knowledgetechnologyuhh/NICO-cad/stl files/ear_right.STL

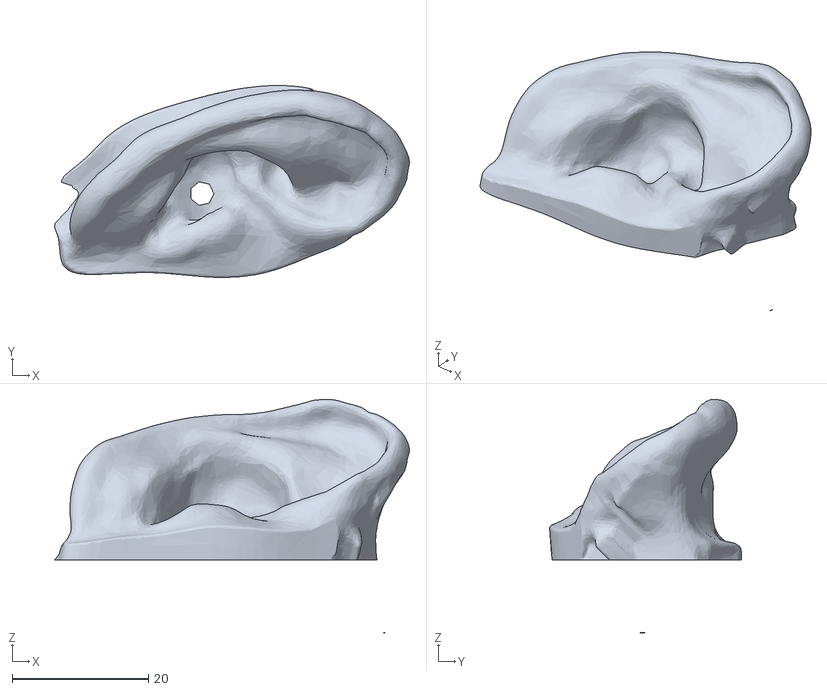
[picture p20: CAD file, 2020-01-28]
stl files/ear_right.STL
52.2 x 28.2 x 34.3
