knowledgetechnologyuhh/NICO-cad/Optimized for SLS/grommet.stl

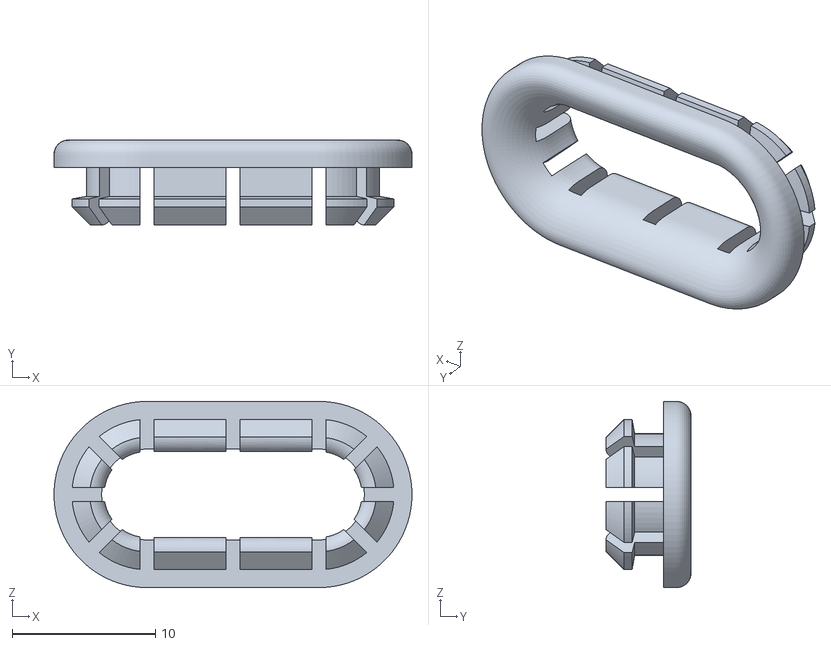
[picture p21: CAD file, 2019-10-23]
Optimized for SLS/grommet.stl
25.0 x 5.93 x 13.0
