knowledgetechnologyuhh/NICO-cad/Optimized for SLS/head_cable_clamp.stl

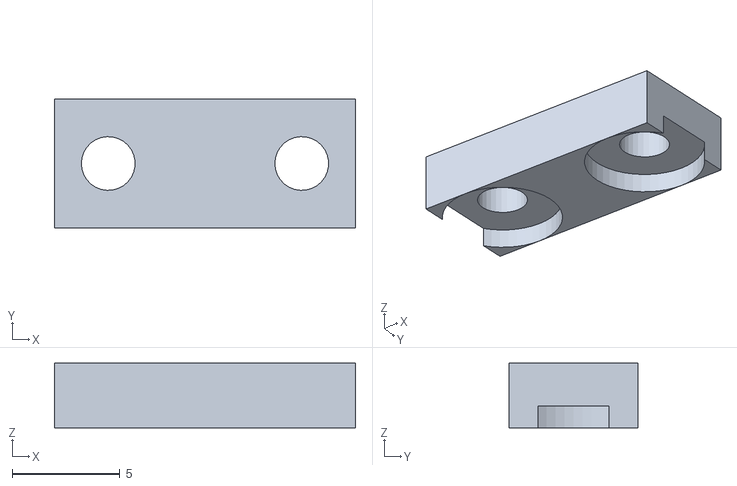
[picture p22: CAD file, 2019-10-23]
Optimized for SLS/head_cable_clamp.stl
14.0 x 6.00 x 3.00
