knowledgetechnologyuhh/NICO-cad/stl files/FR05-S101.stl

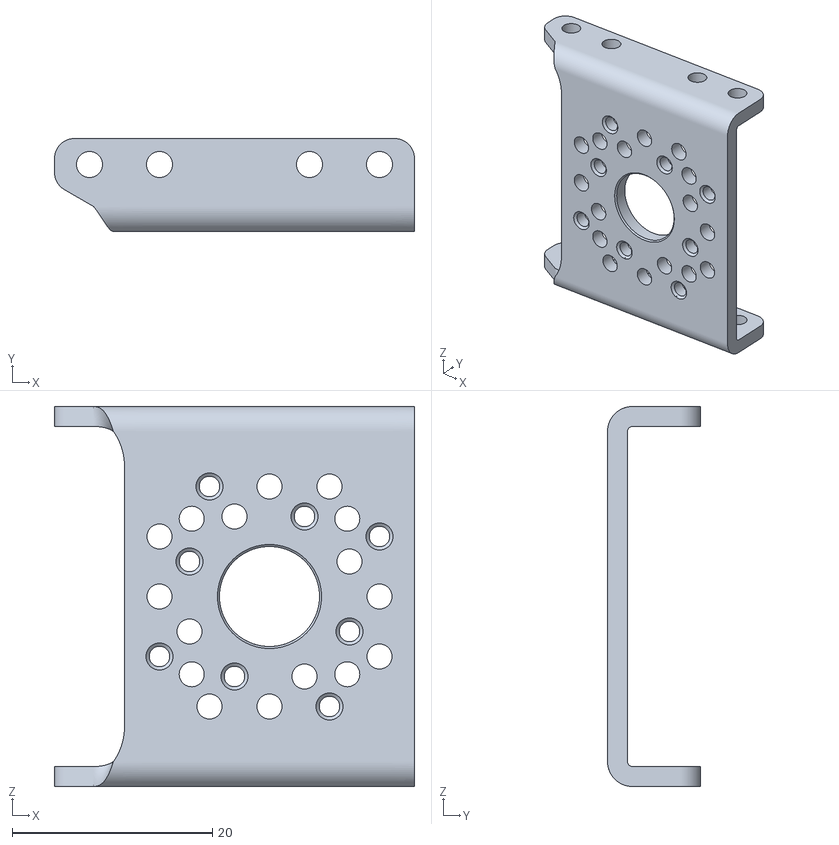
[picture p23: CAD file, 2020-01-28]
stl files/FR05-S101.stl
36.0 x 9.30 x 38.0
