knowledgetechnologyuhh/NICO-cad/Optimized for SLS/upper plate.dxf

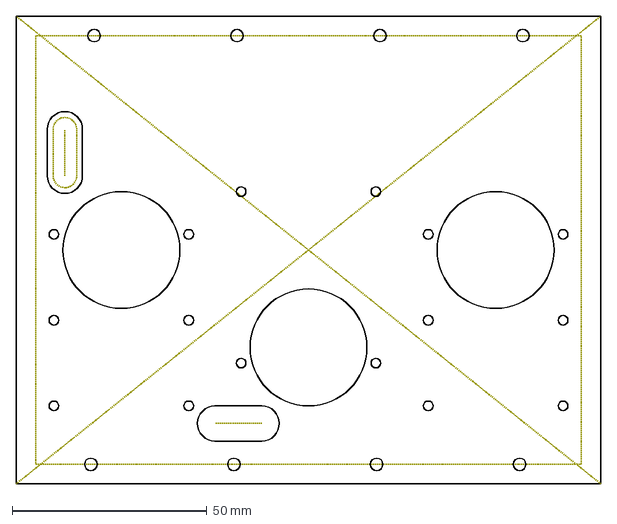
[picture p24: CAD file, 2019-10-23]
Optimized for SLS/upper plate.dxf
150.0 x 120.0 mm
