knowledgetechnologyuhh/NICO-cad/stl files/headnickholder_long.stl

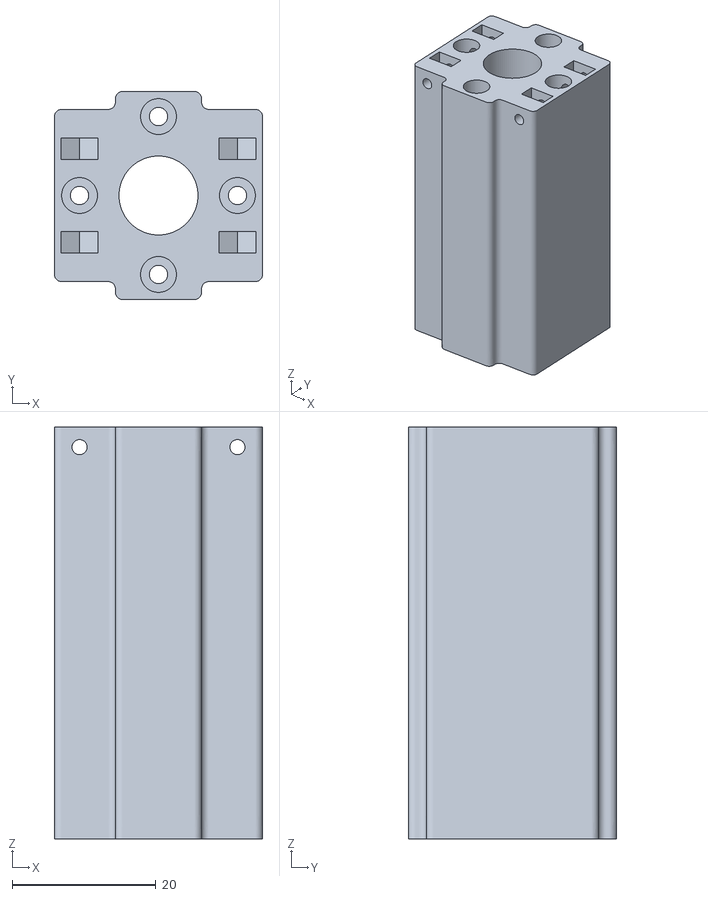
[picture p25: CAD file, 2020-01-28]
stl files/headnickholder_long.stl
29.0 x 29.0 x 57.4
