knowledgetechnologyuhh/NICO-cad/Optimized for SLS/head_support.stl

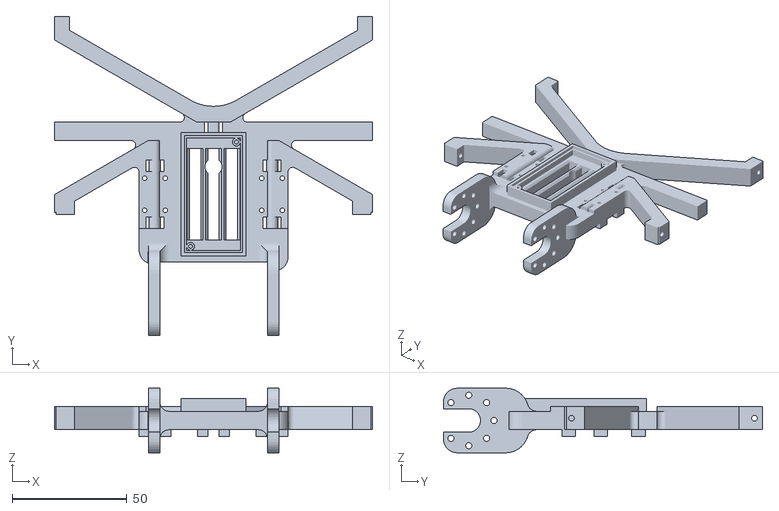
[picture p26: CAD file, 2019-10-23]
Optimized for SLS/head_support.stl
138.7 x 139.1 x 28.2
