knowledgetechnologyuhh/NICO-cad/stl files/lower_arm_thick.stl

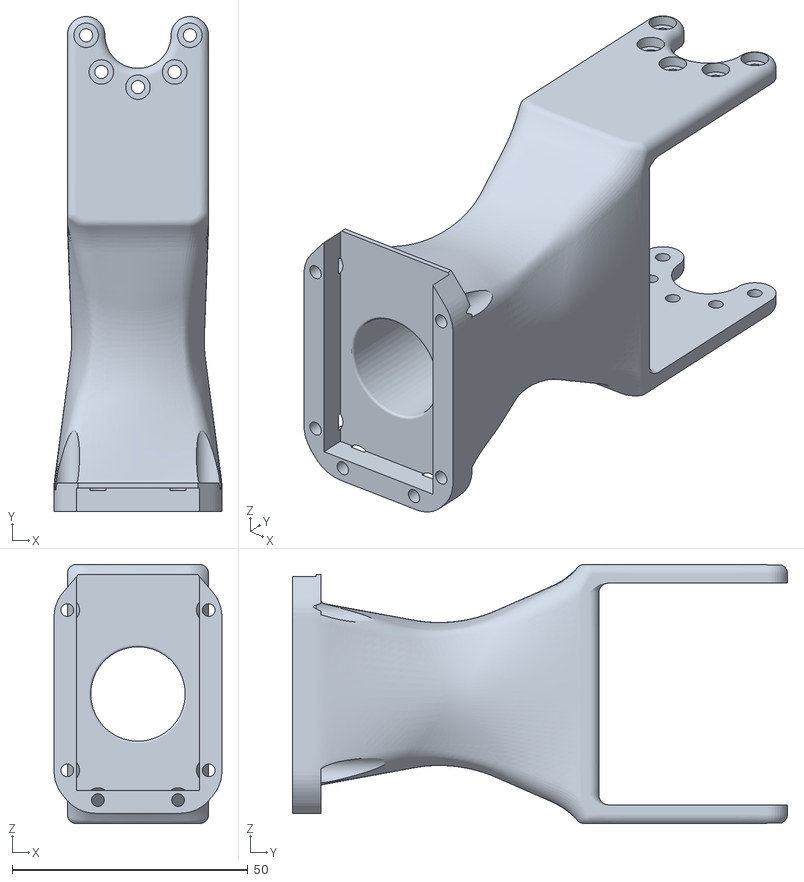
[picture p27: CAD file, 2020-01-28]
stl files/lower_arm_thick.stl
35.6 x 105.0 x 55.0
