knowledgetechnologyuhh/NICO-cad/Optimized for SLS/shoulder.stl

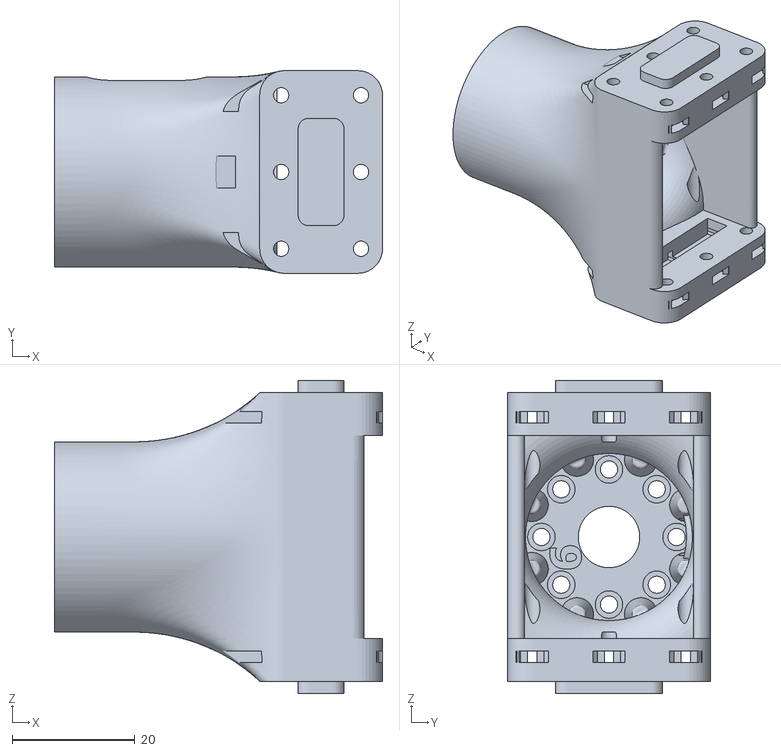
[picture p28: CAD file, 2019-10-23]
Optimized for SLS/shoulder.stl
53.4 x 33.0 x 51.0
