knowledgetechnologyuhh/NICO-cad/stl files/connector.stl

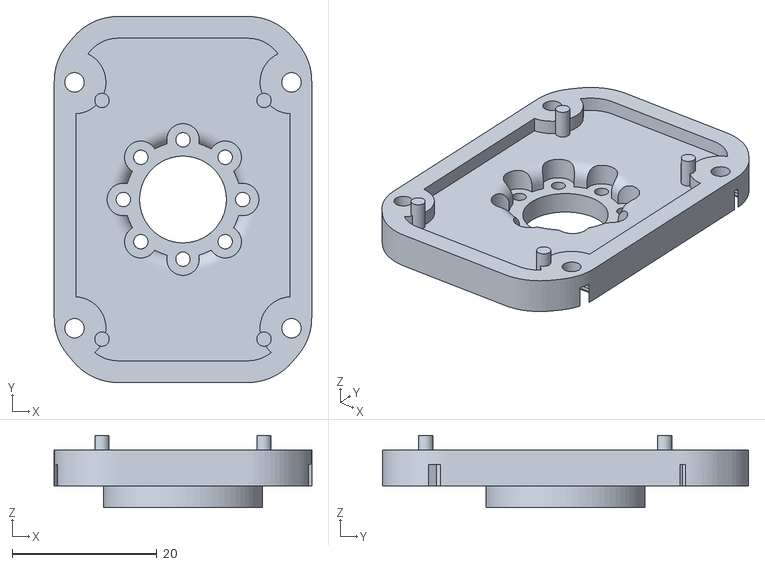
[picture p29: CAD file, 2020-01-28]
stl files/connector.stl
35.6 x 50.6 x 10.0
