knowledgetechnologyuhh/NICO-cad/Optimized for SLS/lower_arm.stl

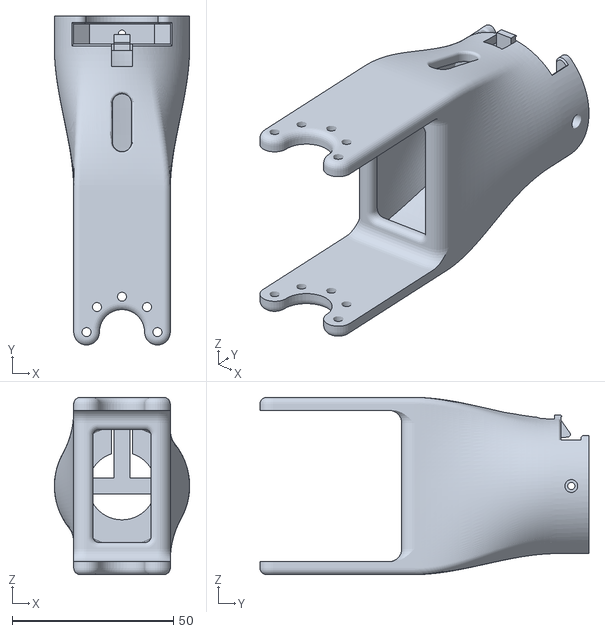
[picture p30: CAD file, 2019-10-23]
Optimized for SLS/lower_arm.stl
42.0 x 102.1 x 55.0
