knowledgetechnologyuhh/NICO-cad/stl files/spider.stl

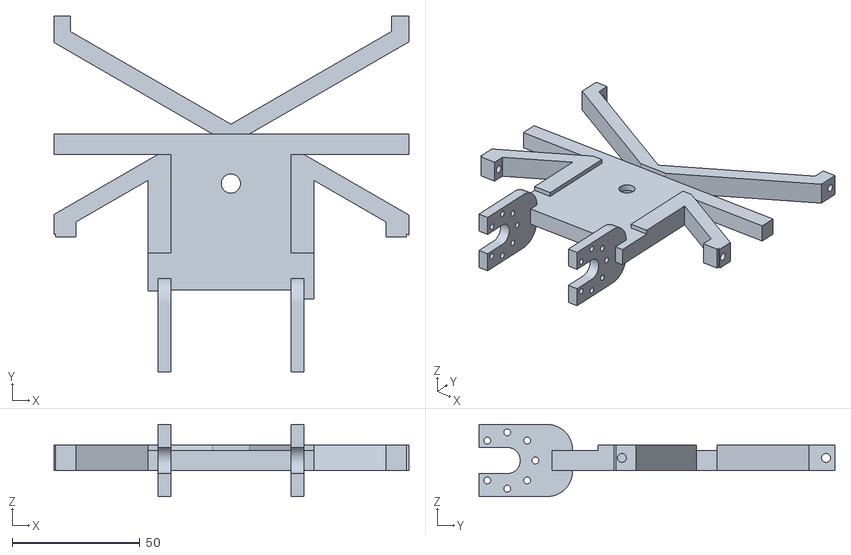
[picture p31: CAD file, 2019-03-22]
stl files/spider.stl
138.7 x 139.1 x 28.2
