knowledgetechnologyuhh/NICO-cad/Optimized for SLS/shoulder_spacer.stl

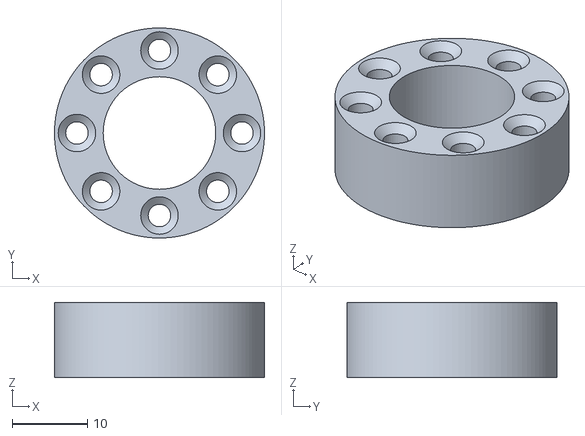
[picture p32: CAD file, 2019-10-23]
Optimized for SLS/shoulder_spacer.stl
28.0 x 28.0 x 10.0
