knowledgetechnologyuhh/NICO-cad/stl files/occiput.stl

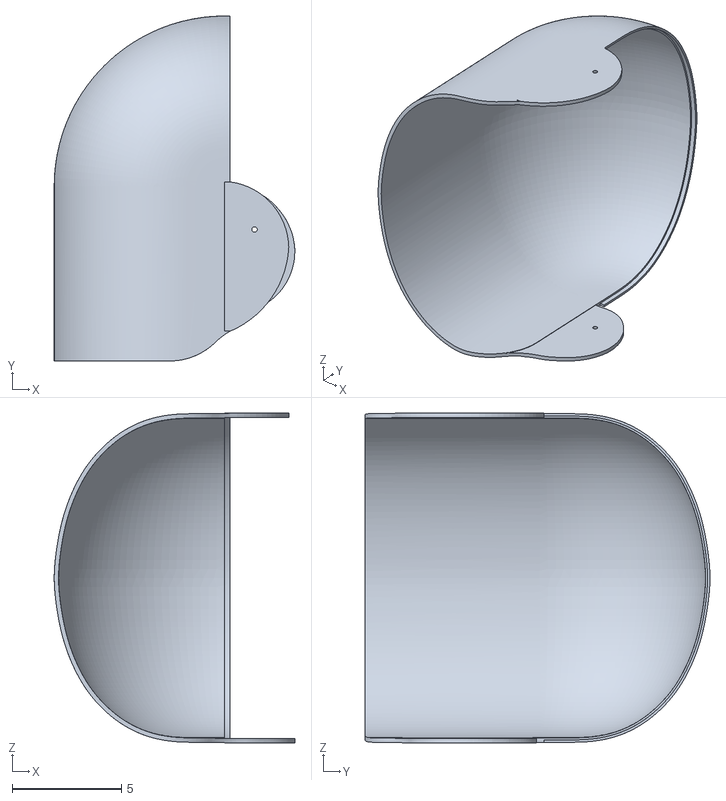
[picture p33: CAD file, 2017-08-02]
stl files/occiput.stl
11.0 x 15.8 x 15.1
