knowledgetechnologyuhh/NICO-cad/Optimized for SLS/RH4D_hand_base.stl

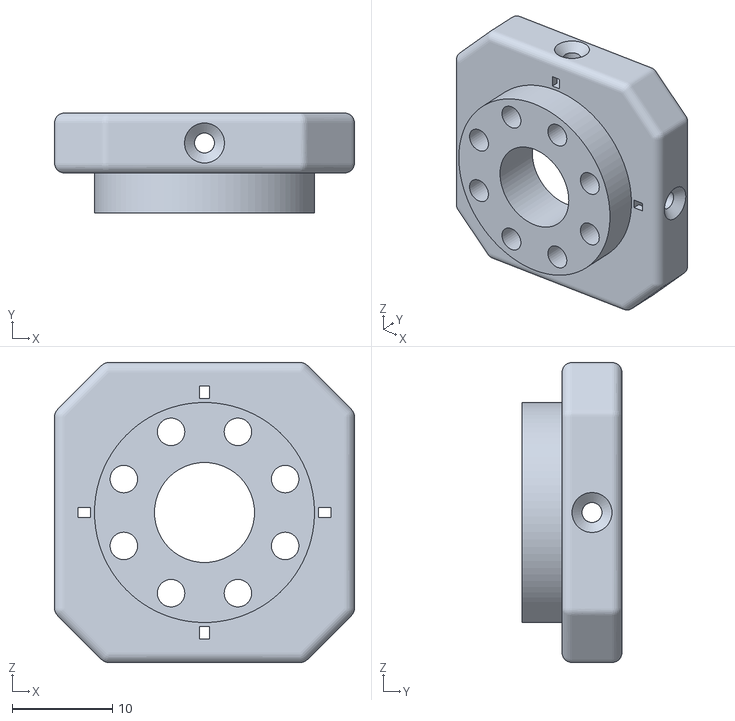
[picture p34: CAD file, 2019-10-23]
Optimized for SLS/RH4D_hand_base.stl
30.0 x 10.0 x 30.0
