knowledgetechnologyuhh/NICO-cad/Optimized for SLS/eyebrows support.stl

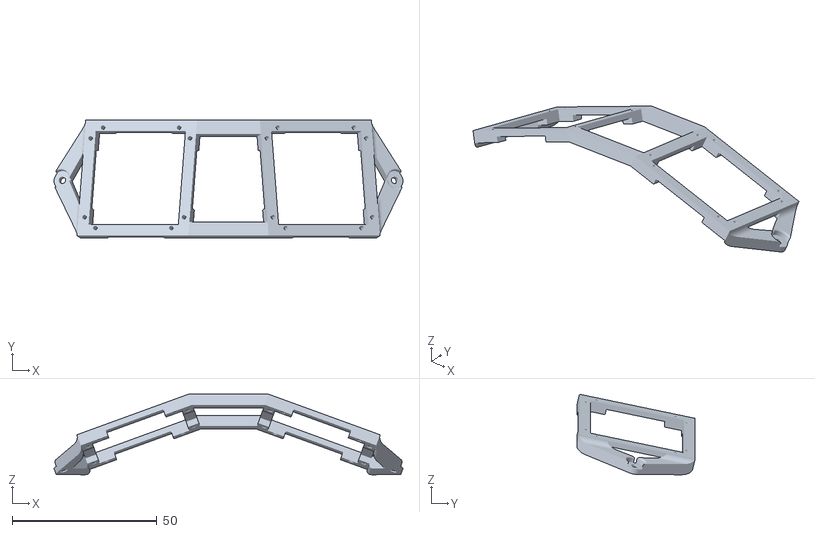
[picture p35: CAD file, 2019-10-23]
Optimized for SLS/eyebrows support.stl
120.6 x 40.9 x 27.9
