knowledgetechnologyuhh/NICO-cad/Optimized for SLS/upper_arm.stl

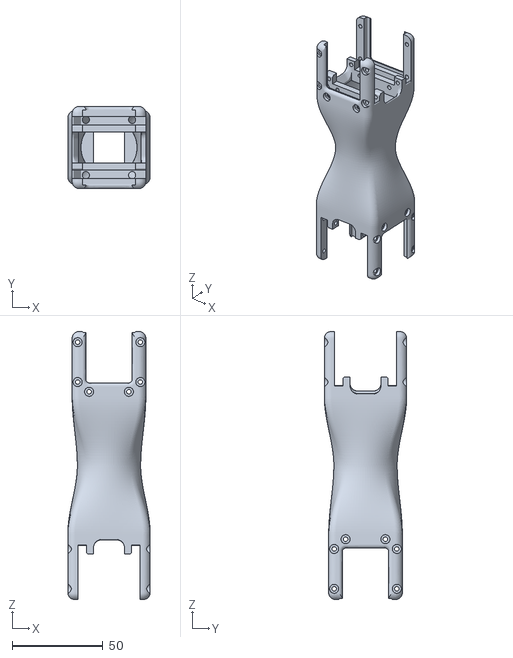
[picture p36: CAD file, 2019-10-23]
Optimized for SLS/upper_arm.stl
45.5 x 45.5 x 148.0
